johnfans/11095_ponding_detection/pegasus/comm_client/wifi_connecter.c

/*
 * Copyright (c) 2022 HiSilicon (Shanghai) Technologies CO., LIMITED.
 * Licensed under the Apache License, Version 2.0 (the "License");
 * you may not use this file except in compliance with the License.
 * You may obtain a copy of the License at
 *
 *     http://www.apache.org/licenses/LICENSE-2.0
 *
 * Unless required by applicable law or agreed to in writing, software
 * distributed under the License is distributed on an "AS IS" BASIS,
 * WITHOUT WARRANTIES OR CONDITIONS OF ANY KIND, either express or implied.
 * See the License for the specific language governing permissions and
 * limitations under the License.
 */

#include "wifi_device.h"
#include "cmsis_os2.h"

#include "lwip/netifapi.h"
#include "lwip/api_shell.h"
#include "net_params.h"

static void PrintLinkedInfo(WifiLinkedInfo* info)
{
    int ret = 0;

    if (!info) {
        return;
    }

    static char macAddress[32] = {0};
    unsigned char* mac = info->bssid;
    if (snprintf_s(macAddress, sizeof(macAddress) + 1, sizeof(macAddress), "%02X:%02X:%02X:%02X:%02X:%02X",
        mac[0], mac[1], mac[2], mac[3], mac[4], mac[5]) < 0) { /* mac地址从0,1,2,3,4,5位 */
            return;
    }
}

static volatile int g_connected = 0;

static void OnWifiConnectionChanged(int state, WifiLinkedInfo* info)
{
    if (!info) return;

    printf("%s %d, state = %d, info = \r\n", __FUNCTION__, __LINE__, state);
    PrintLinkedInfo(info);

    if (state == WIFI_STATE_AVALIABLE) {
        g_connected = 1;
    } else {
        g_connected = 0;
    }
}

static void OnWifiScanStateChanged(int state, int size)
{
    printf("%s %d, state = %X, size = %d\r\n", __FUNCTION__, __LINE__, state, size);
}

static WifiEvent g_defaultWifiEventListener = {
    .OnWifiConnectionChanged = OnWifiConnectionChanged,
    .OnWifiScanStateChanged = OnWifiScanStateChanged
};

static struct netif* g_iface = NULL;

err_t netifapi_set_hostname(struct netif *netif, char *hostname, u8_t namelen);
#define SSID_LEN (11)
#define PSK_LEN (9)
int ConnectToHotspot(void)
{
    WifiDeviceConfig config = {0};

    // 准备AP的配置参数
    strcpy_s(config.ssid, SSID_LEN, PARAM_HOTSPOT_SSID);
    strcpy_s(config.preSharedKey, PSK_LEN, PARAM_HOTSPOT_PSK);
    config.securityType = PARAM_HOTSPOT_TYPE;

    osDelay(10); /* 延时10ms */
    WifiErrorCode errCode;
    int netId = -1;

    errCode = RegisterWifiEvent(&g_defaultWifiEventListener);
    printf("RegisterWifiEvent: %d\r\n", errCode);

    errCode = EnableWifi();
    printf("EnableWifi: %d\r\n", errCode);

    errCode = AddDeviceConfig(&config, &netId);
    printf("AddDeviceConfig: %d\r\n", errCode);

    g_connected = 0;
    errCode = ConnectTo(netId);
    printf("ConnectTo(%d): %d\r\n", netId, errCode);

    while (!g_connected) { // wait until connect to AP
        osDelay(10); /* 持续10ms去连接AP */
    }
    printf("g_connected: %d\r\n", g_connected);

    g_iface = netifapi_netif_find("wlan0");
    if (g_iface) {
        char* hostname = "hispark";
        err_t ret = netifapi_set_hostname(g_iface, hostname, strlen(hostname));
        printf("netifapi_set_hostname: %d\r\n", ret);

        ret = netifapi_dhcp_start(g_iface);
        printf("netifapi_dhcp_start: %d\r\n", ret);

        osDelay(100); // wait DHCP server give me IP 100
#if 1
        ret = netifapi_netif_common(g_iface, dhcp_clients_info_show, NULL);
        printf("netifapi_netif_common: %d\r\n", ret);
#else
#endif
    }
    return netId;
}

void DisconnectWithHotspot(int netId)
{
    if (g_iface) {
        err_t ret = netifapi_dhcp_stop(g_iface);
        printf("netifapi_dhcp_stop: %d\r\n", ret);
    }

    WifiErrorCode errCode = Disconnect(); // disconnect with your AP
    printf("Disconnect: %d\r\n", errCode);

    errCode = UnRegisterWifiEvent(&g_defaultWifiEventListener);
    printf("UnRegisterWifiEvent: %d\r\n", errCode);

    RemoveDevice(netId); // remove AP config
    printf("RemoveDevice: %d\r\n", errCode);

    errCode = DisableWifi();
    printf("DisableWifi: %d\r\n", errCode);
}
